aryan-r22/SAATHI_BAND/Prototype_3DModel/w1.png

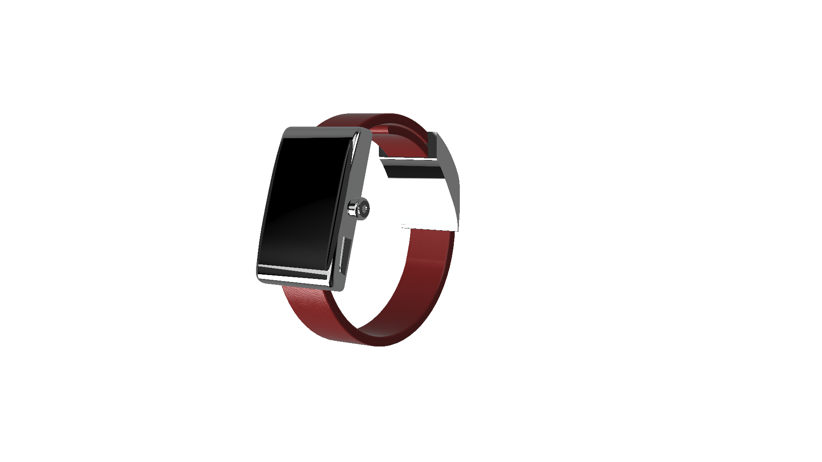
Prototype_3DModel/w1.png
