aryan-r22/SAATHI_BAND/Prototype_3DModel/w2.png

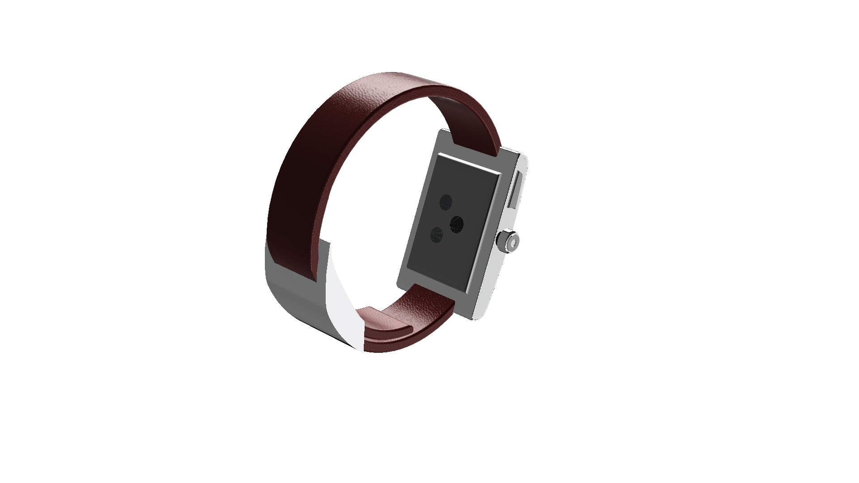
Prototype_3DModel/w2.png
